sneakylizard123-4/bitcoinMiner/kicad/3d/PLCC6_LED_3_5X3_4X2_8_CRW.step

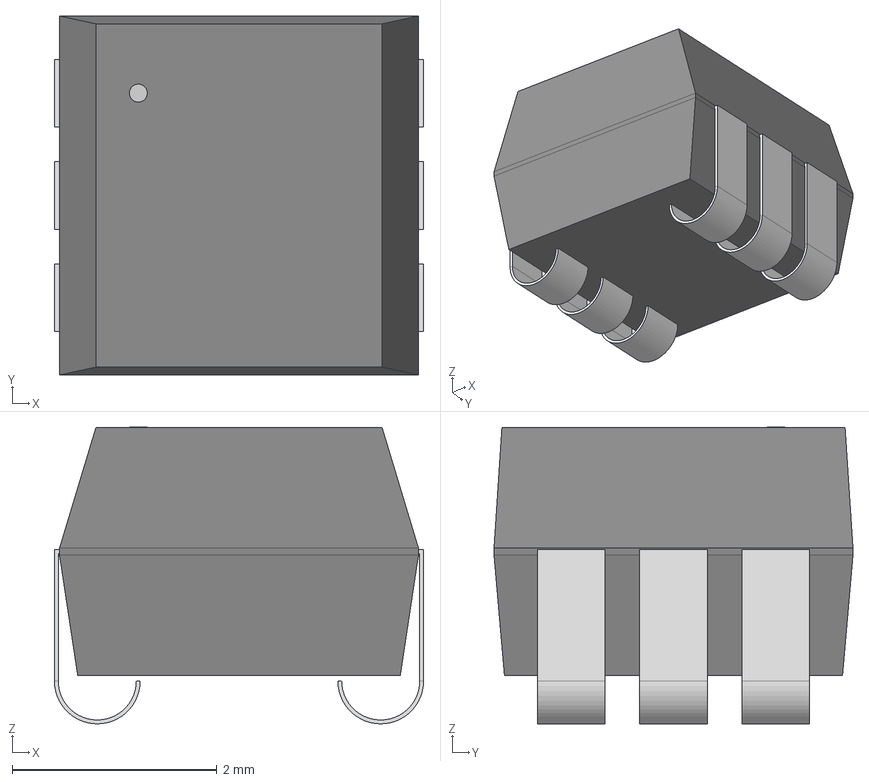
[picture p22: CAD file, 2026-02-14]
kicad/3d/PLCC6_LED_3_5X3_4X2_8_CRW.step
3.61 x 3.51 x 2.90 mm
