sneakylizard123-4/bitcoinMiner/kicad/3d/CX3225SB16000H0FLJCC.STEP

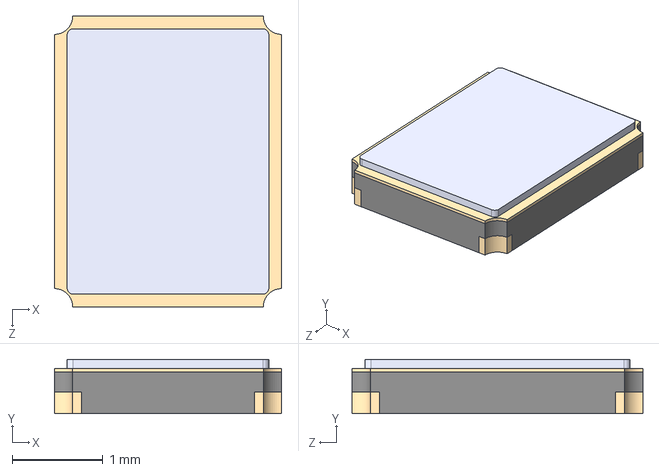
[picture p25: CAD file, 2026-02-14]
kicad/3d/CX3225SB16000H0FLJCC.STEP
2.50 x 0.6 x 3.20 mm
