sneakylizard123-4/bitcoinMiner/kicad/3d/21-0164B_L622-1_MXM.step

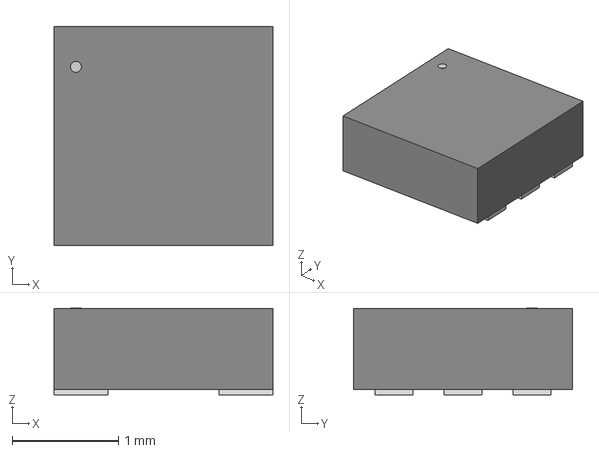
[picture p27: CAD file, 2026-02-14]
kicad/3d/21-0164B_L622-1_MXM.step
2.06 x 2.06 x 0.815 mm
