sneakylizard123-4/bitcoinMiner/kicad/3d/IHLP2020CZ.step

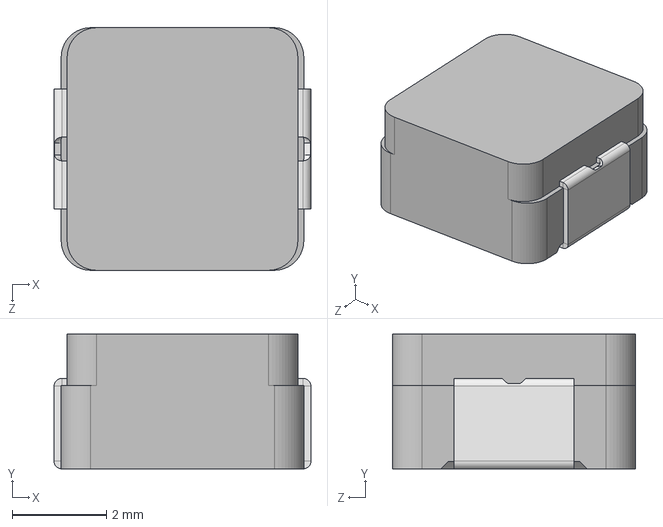
[picture p28: CAD file, 2026-02-14]
kicad/3d/IHLP2020CZ.step
5.45 x 2.86 x 5.15 mm
