sneakylizard123-4/bitcoinMiner/kicad/3d/BM1368xx.stp

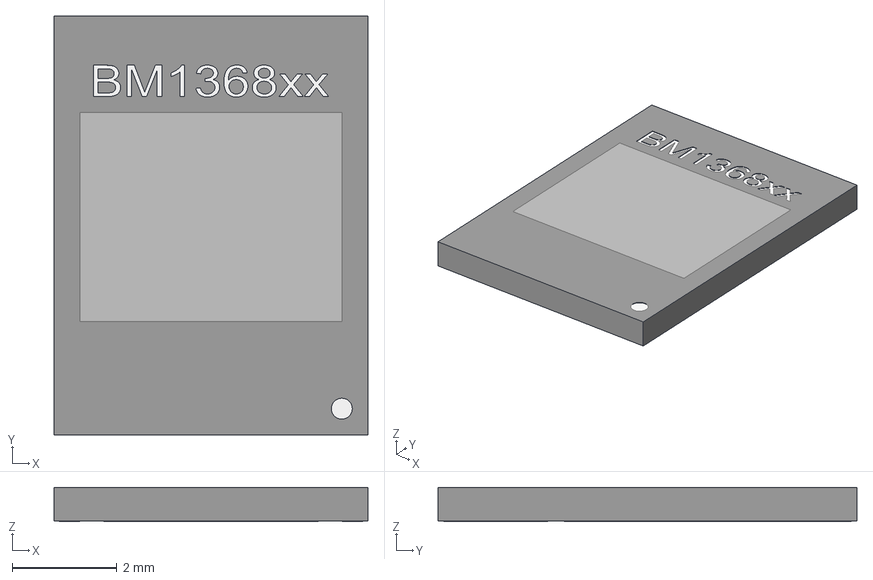
[picture p29: CAD file, 2026-02-14]
kicad/3d/BM1368xx.stp
6.00 x 8.00 x 0.65 mm
