sneakylizard123-4/bitcoinMiner/kicad/3d/BM04B-SRSS-TBT(LF)(SN)--3DModel-STEP-56544.STEP

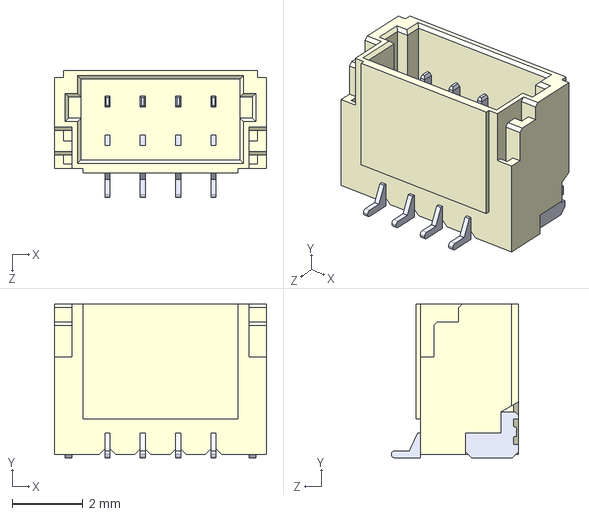
[picture p30: CAD file, 2026-02-14]
kicad/3d/BM04B-SRSS-TBT(LF)(SN)--3DModel-STEP-56544.STEP
6.00 x 4.35 x 3.60 mm
