sneakylizard123-4/bitcoinMiner/kicad/3d/DQG0008A.stp

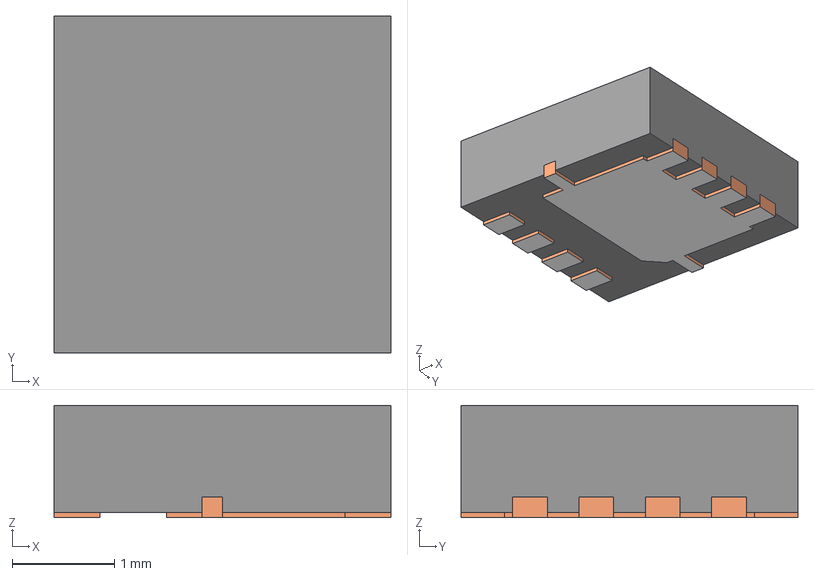
[picture p31: CAD file, 2026-02-14]
kicad/3d/DQG0008A.stp
3.30 x 3.30 x 1.10 mm
BODY-SON
FRAME-DQG0008A
PIN1-ID
