sneakylizard123-4/bitcoinMiner/kicad/3d/CS1213AG-tr.stp

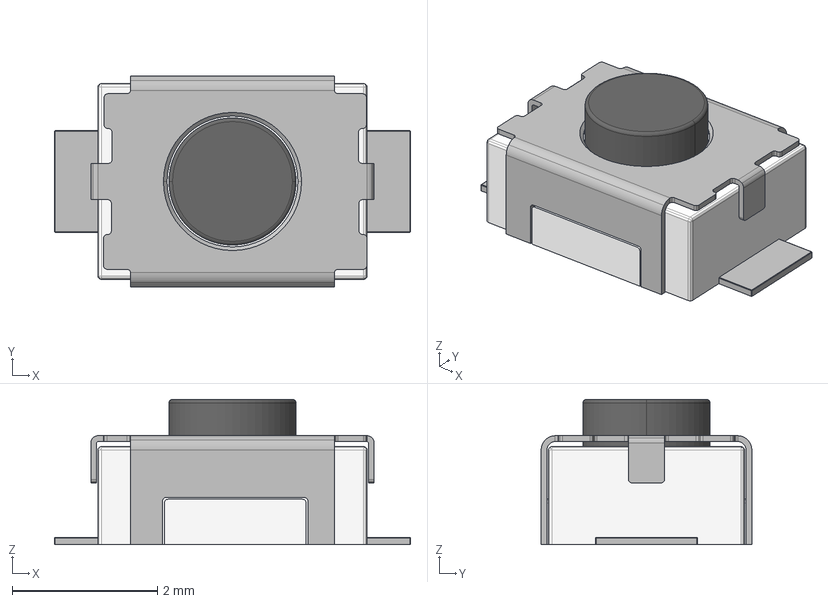
[picture p33: CAD file, 2026-02-14]
kicad/3d/CS1213AG-tr.stp
4.90 x 2.90 x 2.00 mm
