sneakylizard123-4/bitcoinMiner/kicad/3d/CUI_DEVICES_PJ-037AH.step

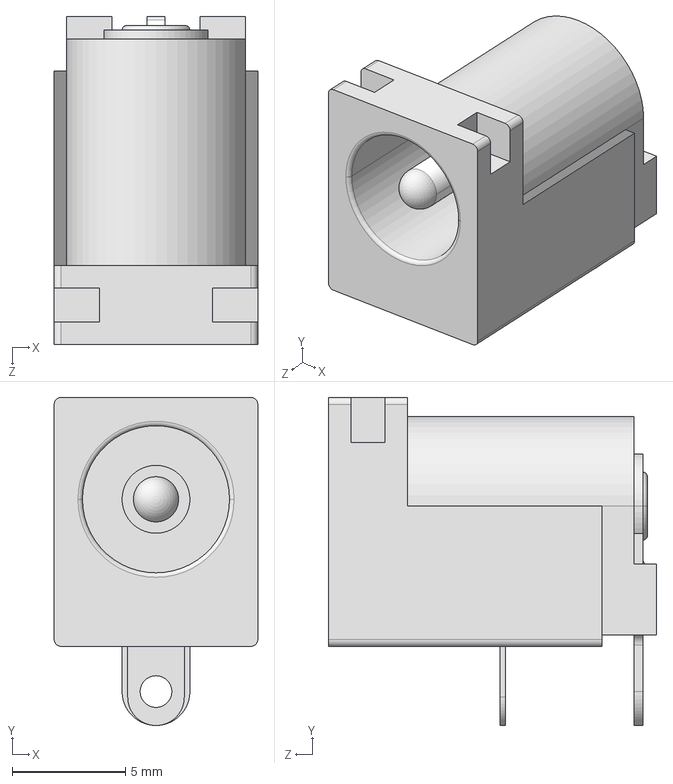
[picture p34: CAD file, 2026-02-14]
kicad/3d/CUI_DEVICES_PJ-037AH.step
9.00 x 14.5 x 14.5 mm
