sneakylizard123-4/bitcoinMiner/kicad/3d/TPS546D24ARVFR.step

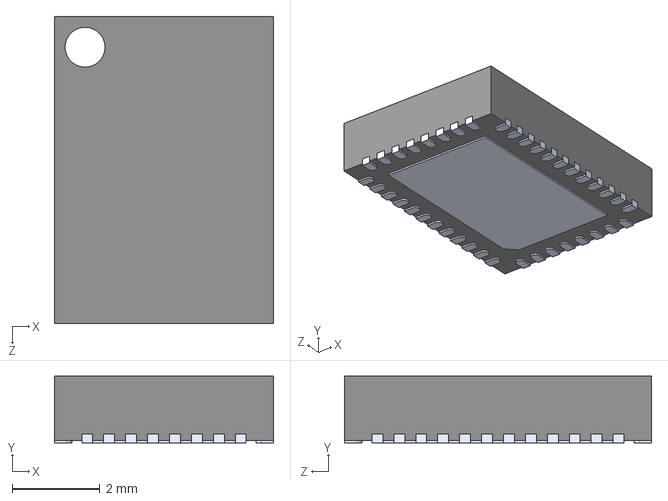
[picture p35: CAD file, 2026-02-14]
kicad/3d/TPS546D24ARVFR.step
5.00 x 1.52 x 7.00 mm
