sneakylizard123-4/bitcoinMiner/kicad/3d/DQH0008A.stp

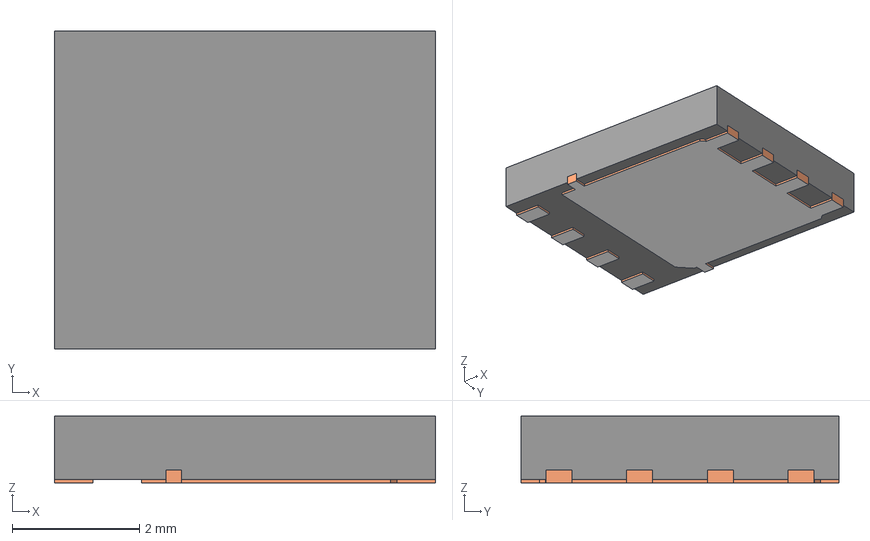
[picture p36: CAD file, 2026-02-14]
kicad/3d/DQH0008A.stp
6.00 x 5.00 x 1.05 mm
BODY-SON
FRAME-DQH0008A
PIN1-ID
