sneakylizard123-4/bitcoinMiner/kicad/3d/TXB0104RGYR.STEP

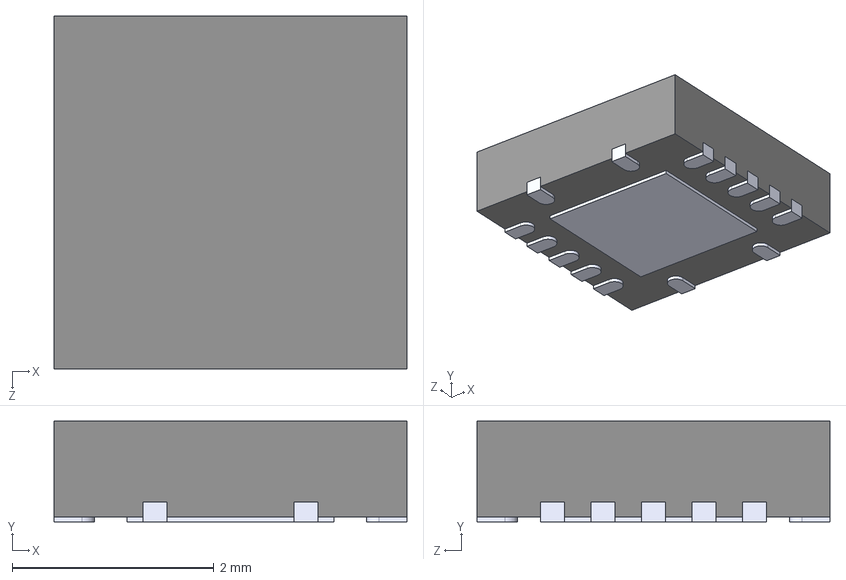
[picture p38: CAD file, 2026-02-14]
kicad/3d/TXB0104RGYR.STEP
3.50 x 1.00 x 3.50 mm
