sneakylizard123-4/bitcoinMiner/kicad/3d/SMV_z90.stp

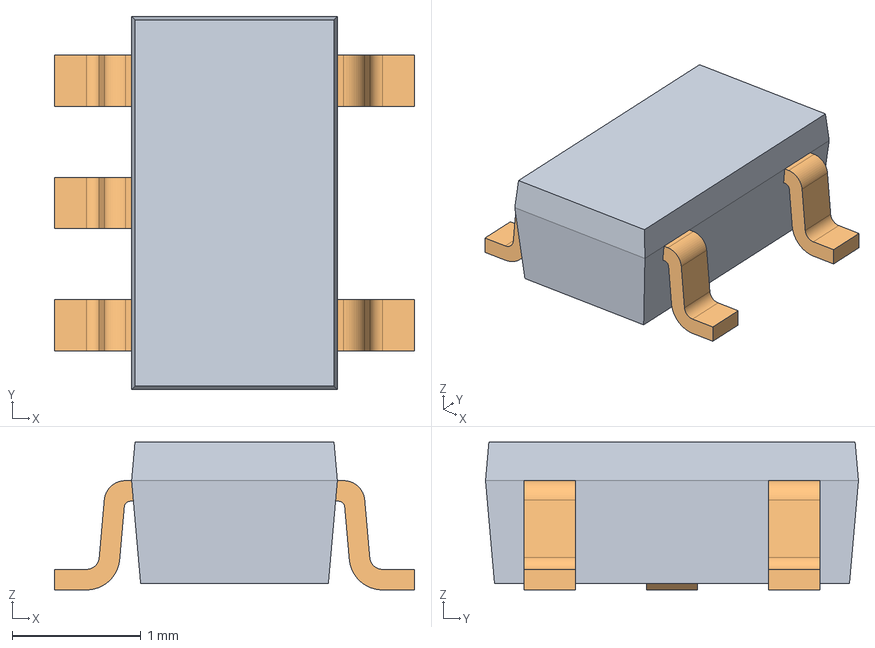
[picture p39: CAD file, 2026-02-14]
kicad/3d/SMV_z90.stp
2.80 x 2.90 x 1.15 mm
