sneakylizard123-4/bitcoinMiner/kicad/3d/SW_CS1213AGF260_CRS.step

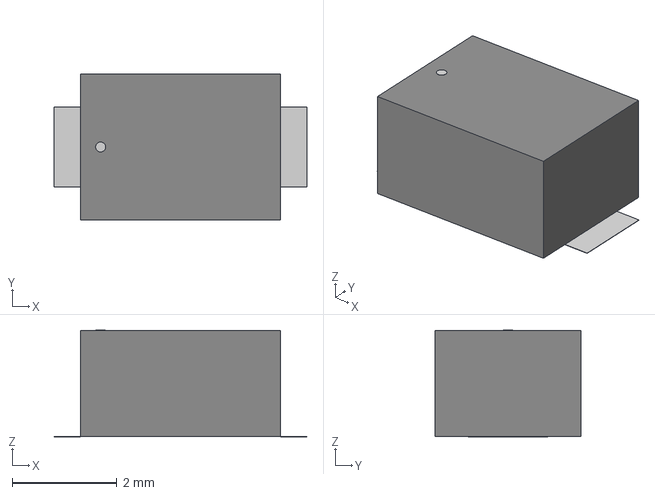
[picture p41: CAD file, 2026-02-14]
kicad/3d/SW_CS1213AGF260_CRS.step
4.83 x 2.79 x 2.04 mm
