sneakylizard123-4/bitcoinMiner/kicad/3d/oscillator3.2x2.5.step

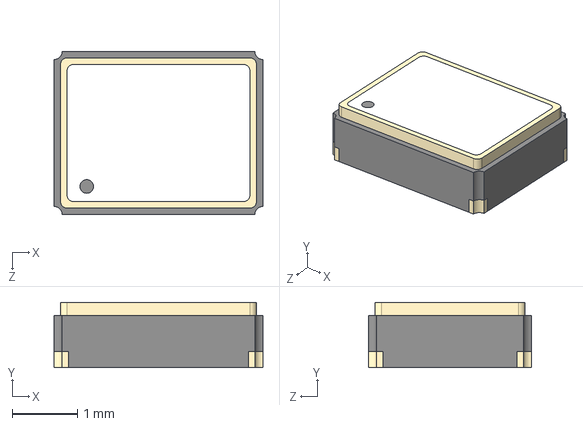
[picture p42: CAD file, 2026-02-14]
kicad/3d/oscillator3.2x2.5.step
3.20 x 1.00 x 2.50 mm
