sneakylizard123-4/bitcoinMiner/kicad/3d/SOT-23-5_M5_MCH.step

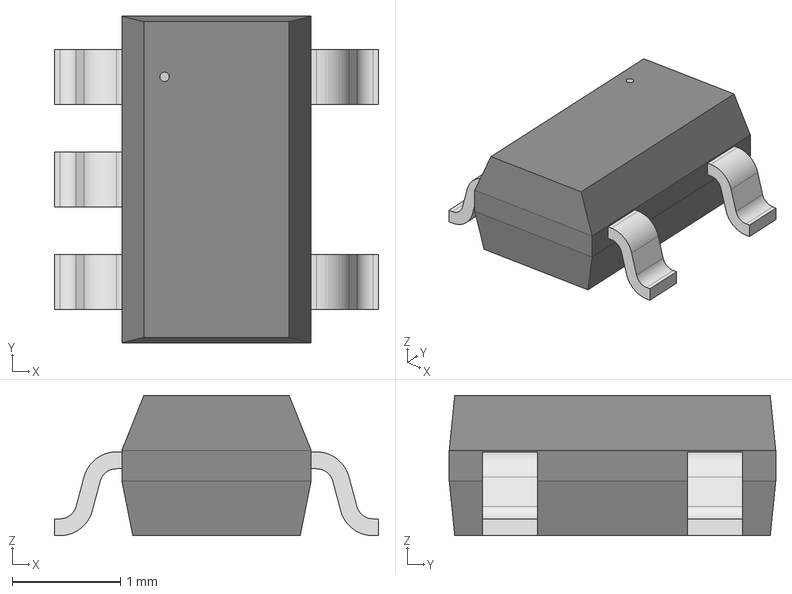
[picture p44: CAD file, 2026-02-14]
kicad/3d/SOT-23-5_M5_MCH.step
3.00 x 3.02 x 1.30 mm
