sneakylizard123-4/bitcoinMiner/firmware/main/power/vcore.c

#include "esp_log.h"
#include <math.h>
#include <stdio.h>
#include "freertos/FreeRTOS.h"
#include "freertos/task.h"

#include "DS4432U.h"
#include "INA260.h"
#include "TPS546.h"
#include "nvs_config.h"
#include "adc.h"
#include "driver/gpio.h"
#include "global_state.h"
#include "device_config.h"
#include "vcore.h"

#define GPIO_ASIC_ENABLE CONFIG_GPIO_ASIC_ENABLE
#define GPIO_PLUG_SENSE CONFIG_GPIO_PLUG_SENSE

static const char *TAG = "vcore";
static bool vcore_initialized = false;

static void log_tps546_config(const FamilyConfig *family, const TPS546_CONFIG *config)
{
    ESP_LOGI(TAG, "Selected TPS546 config for family=%s id=%d voltage_domains=%u",
             family->name, (int)family->id, (unsigned)family->voltage_domains);
    ESP_LOGI(TAG, "TPS546 init core: phase=0x%02X stack=0x%04X sync=0x%02X scale=%.3f vout=%.2f min=%.2f max=%.2f",
             config->TPS546_INIT_PHASE,
             config->TPS546_INIT_STACK_CONFIG,
             config->TPS546_INIT_SYNC_CONFIG,
             config->TPS546_INIT_SCALE_LOOP,
             config->TPS546_INIT_VOUT_COMMAND,
             config->TPS546_INIT_VOUT_MIN,
             config->TPS546_INIT_VOUT_MAX);
    ESP_LOGI(TAG, "TPS546 init VIN: on=%.2f off=%.2f uv_warn=%.2f ov_fault=%.2f",
             config->TPS546_INIT_VIN_ON,
             config->TPS546_INIT_VIN_OFF,
             config->TPS546_INIT_VIN_UV_WARN_LIMIT,
             config->TPS546_INIT_VIN_OV_FAULT_LIMIT);
    ESP_LOGI(TAG, "TPS546 init IOUT: warn=%.2f fault=%.2f",
             config->TPS546_INIT_IOUT_OC_WARN_LIMIT,
             config->TPS546_INIT_IOUT_OC_FAULT_LIMIT);
    ESP_LOGI(TAG, "TPS546 init COMPENSATION_CONFIG: %02X %02X %02X %02X %02X",
             config->TPS546_INIT_COMPENSATION_CONFIG[0],
             config->TPS546_INIT_COMPENSATION_CONFIG[1],
             config->TPS546_INIT_COMPENSATION_CONFIG[2],
             config->TPS546_INIT_COMPENSATION_CONFIG[3],
             config->TPS546_INIT_COMPENSATION_CONFIG[4]);
}

static TPS546_CONFIG get_tps546_config(const FamilyConfig * family)
{
    TPS546_CONFIG config = family->tps546_config ? *family->tps546_config : TPS546_CONFIG_DEFAULT;

    if (nvs_config_has_key(NVS_CONFIG_TPS546_PHASE)) {
        config.TPS546_INIT_PHASE = (uint8_t)nvs_config_get_u16(NVS_CONFIG_TPS546_PHASE);
    }
    if (nvs_config_has_key(NVS_CONFIG_TPS546_VIN_ON)) {
        config.TPS546_INIT_VIN_ON = nvs_config_get_float(NVS_CONFIG_TPS546_VIN_ON);
    }
    if (nvs_config_has_key(NVS_CONFIG_TPS546_VIN_OFF)) {
        config.TPS546_INIT_VIN_OFF = nvs_config_get_float(NVS_CONFIG_TPS546_VIN_OFF);
    }
    if (nvs_config_has_key(NVS_CONFIG_TPS546_VIN_UV_WARN)) {
        config.TPS546_INIT_VIN_UV_WARN_LIMIT = nvs_config_get_float(NVS_CONFIG_TPS546_VIN_UV_WARN);
    }
    if (nvs_config_has_key(NVS_CONFIG_TPS546_VIN_OV_FAULT)) {
        config.TPS546_INIT_VIN_OV_FAULT_LIMIT = nvs_config_get_float(NVS_CONFIG_TPS546_VIN_OV_FAULT);
    }
    if (nvs_config_has_key(NVS_CONFIG_TPS546_SCALE_LOOP)) {
        config.TPS546_INIT_SCALE_LOOP = nvs_config_get_float(NVS_CONFIG_TPS546_SCALE_LOOP);
    }
    if (nvs_config_has_key(NVS_CONFIG_TPS546_VOUT_MIN)) {
        config.TPS546_INIT_VOUT_MIN = nvs_config_get_float(NVS_CONFIG_TPS546_VOUT_MIN);
    }
    if (nvs_config_has_key(NVS_CONFIG_TPS546_VOUT_MAX)) {
        config.TPS546_INIT_VOUT_MAX = nvs_config_get_float(NVS_CONFIG_TPS546_VOUT_MAX);
    }
    if (nvs_config_has_key(NVS_CONFIG_TPS546_VOUT_COMMAND)) {
        config.TPS546_INIT_VOUT_COMMAND = nvs_config_get_float(NVS_CONFIG_TPS546_VOUT_COMMAND);
    }
    if (nvs_config_has_key(NVS_CONFIG_TPS546_IOUT_OC_WARN)) {
        config.TPS546_INIT_IOUT_OC_WARN_LIMIT = nvs_config_get_float(NVS_CONFIG_TPS546_IOUT_OC_WARN);
    }
    if (nvs_config_has_key(NVS_CONFIG_TPS546_IOUT_OC_FAULT)) {
        config.TPS546_INIT_IOUT_OC_FAULT_LIMIT = nvs_config_get_float(NVS_CONFIG_TPS546_IOUT_OC_FAULT);
    }
    if (nvs_config_has_key(NVS_CONFIG_TPS546_STACK_CONFIG)) {
        config.TPS546_INIT_STACK_CONFIG = nvs_config_get_u16(NVS_CONFIG_TPS546_STACK_CONFIG);
    }
    if (nvs_config_has_key(NVS_CONFIG_TPS546_SYNC_CONFIG)) {
        config.TPS546_INIT_SYNC_CONFIG = (uint8_t)nvs_config_get_u16(NVS_CONFIG_TPS546_SYNC_CONFIG);
    }
    if (nvs_config_has_key(NVS_CONFIG_TPS546_FREQUENCY)) {
        config.TPS546_INIT_FREQUENCY = nvs_config_get_u16(NVS_CONFIG_TPS546_FREQUENCY);
    }

    log_tps546_config(family, &config);
    return config;
}
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
